fabiobrasileiroo/silakka54-fabio-custom/01-final/previews/preview-carry-67mm.png

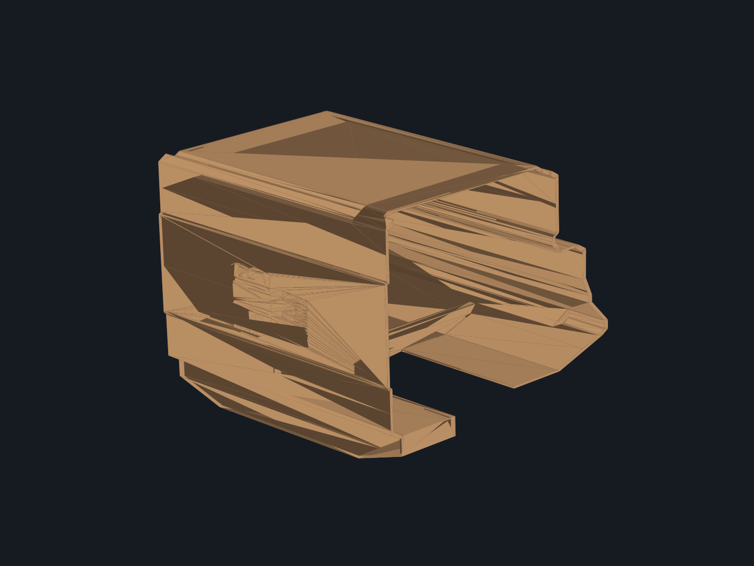
01-final/previews/preview-carry-67mm.png
