fabiobrasileiroo/silakka54-fabio-custom/docs/01-final/previews/preview-base-L.png

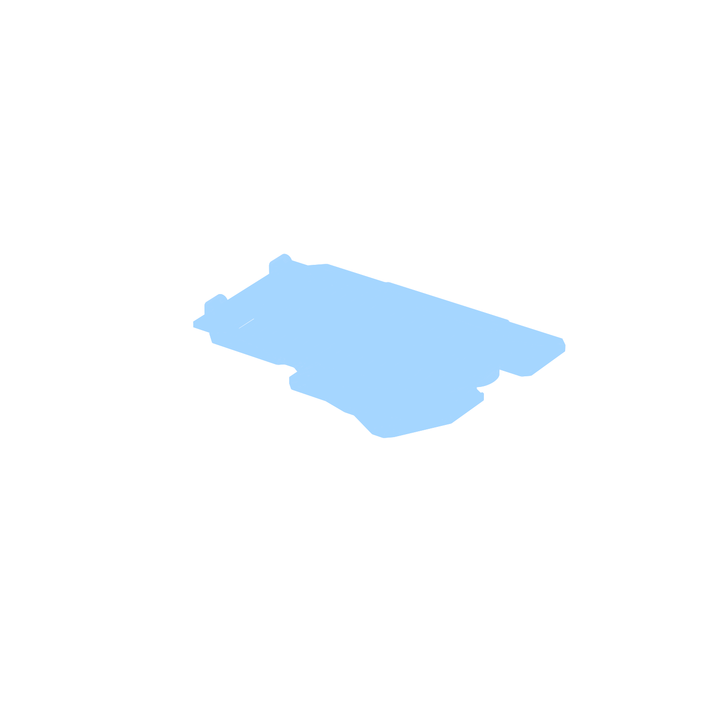
docs/01-final/previews/preview-base-L.png
