fabiobrasileiroo/silakka54-fabio-custom/docs/01-final/previews/preview-carry-case.png

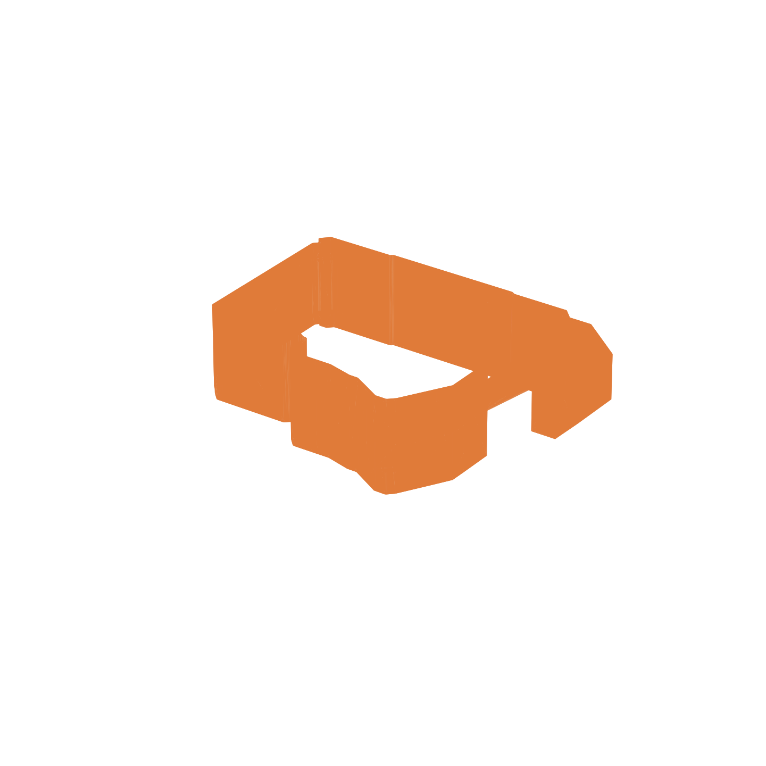
docs/01-final/previews/preview-carry-case.png
