fabiobrasileiroo/silakka54-fabio-custom/docs/01-final/previews/preview-carry-check-engrave.png

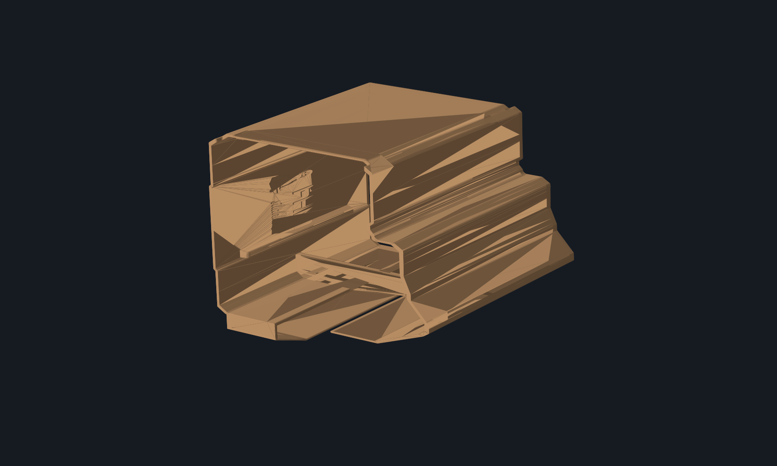
docs/01-final/previews/preview-carry-check-engrave.png
