fabiobrasileiroo/silakka54-fabio-custom/docs/01-final/previews/preview-carry-check-mirror.png

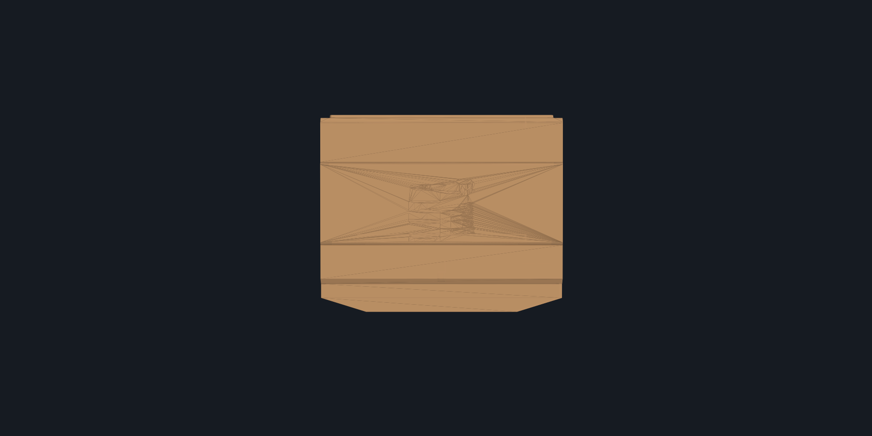
docs/01-final/previews/preview-carry-check-mirror.png
