fabiobrasileiroo/silakka54-fabio-custom/docs/01-final/previews/preview-cover-plaque-RH.png

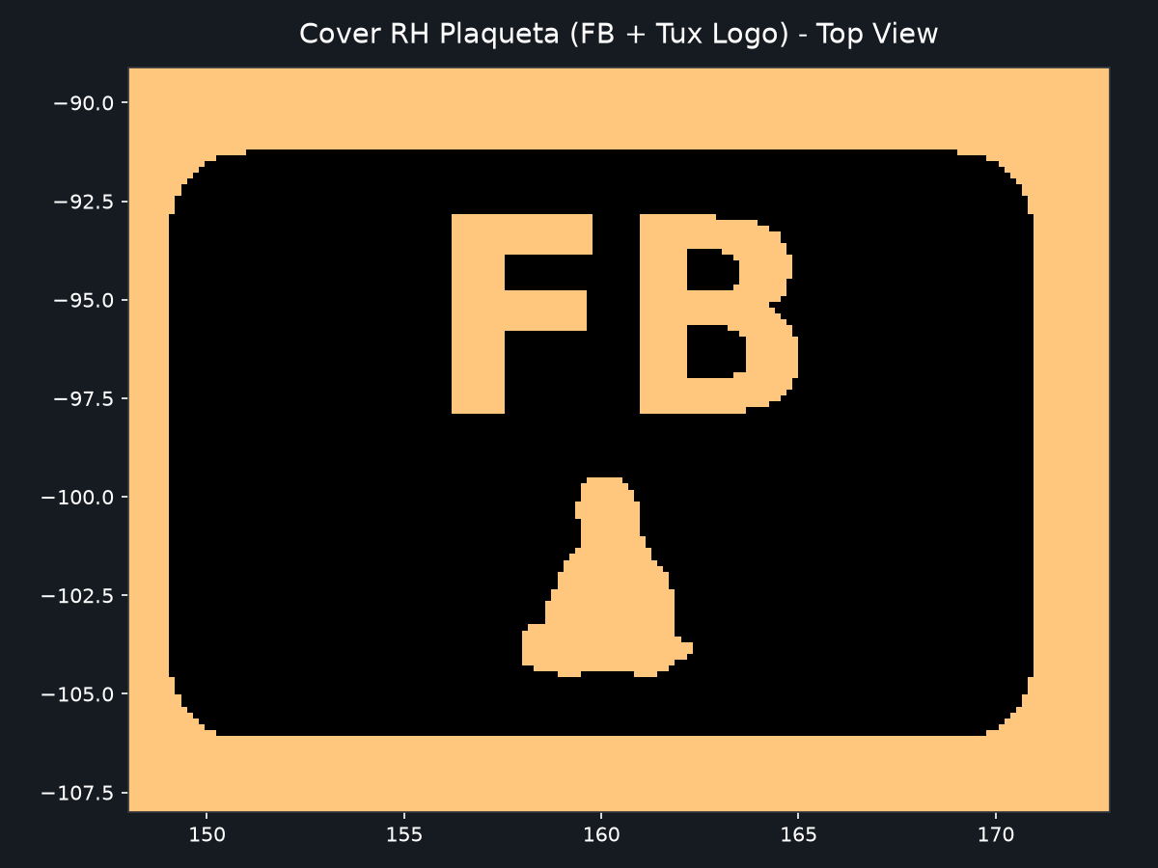
docs/01-final/previews/preview-cover-plaque-RH.png
