fabiobrasileiroo/silakka54-fabio-custom/docs/01-final/previews/preview-FB-Tux-linux-LH.png

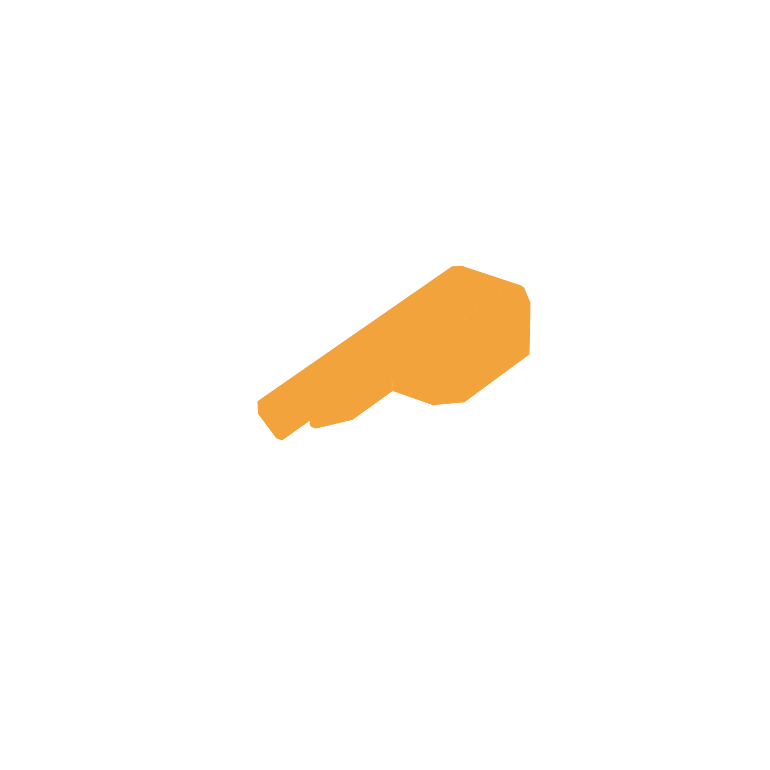
docs/01-final/previews/preview-FB-Tux-linux-LH.png
