fabiobrasileiroo/silakka54-fabio-custom/docs/01-final/previews/preview-FB-Tux-linux-RH.png

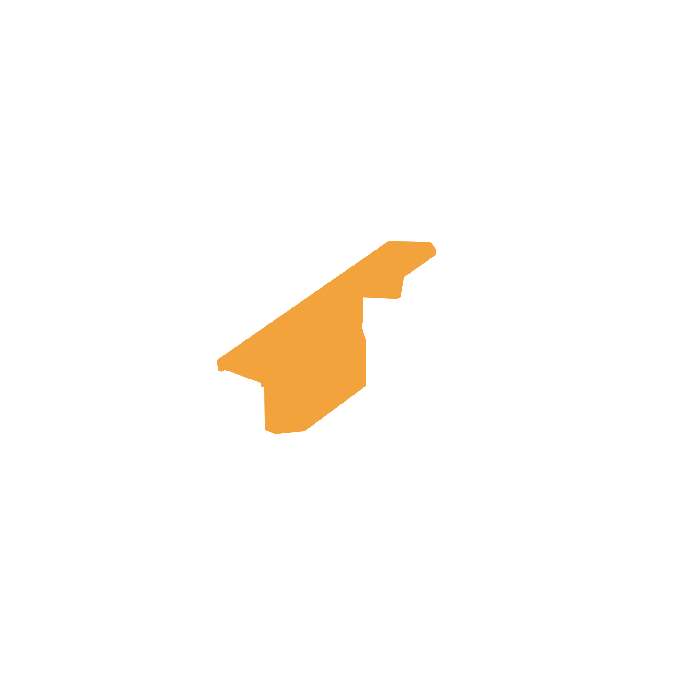
docs/01-final/previews/preview-FB-Tux-linux-RH.png
