fabiobrasileiroo/silakka54-fabio-custom/docs/01-final/previews/preview-inner-frame.png

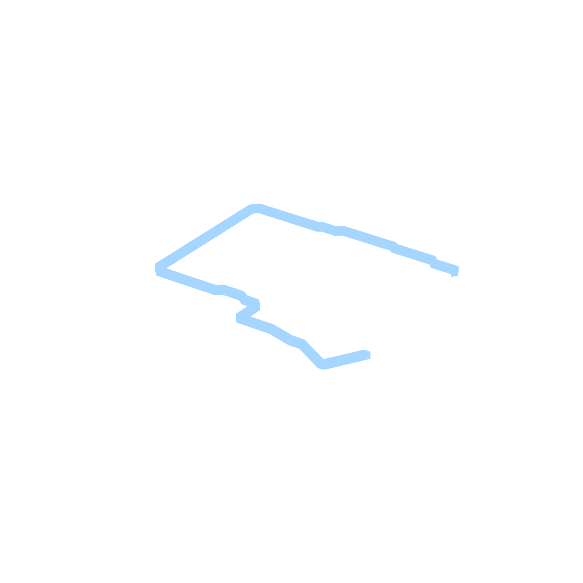
docs/01-final/previews/preview-inner-frame.png
