fabiobrasileiroo/silakka54-fabio-custom/docs/01-final/previews/preview-java-RH.png

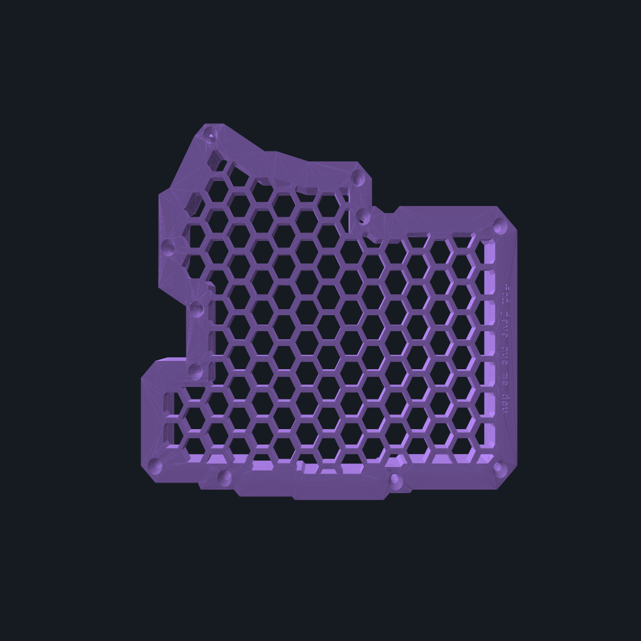
docs/01-final/previews/preview-java-RH.png
