fabiobrasileiroo/silakka54-fabio-custom/docs/01-final/previews/preview-js-LH.png

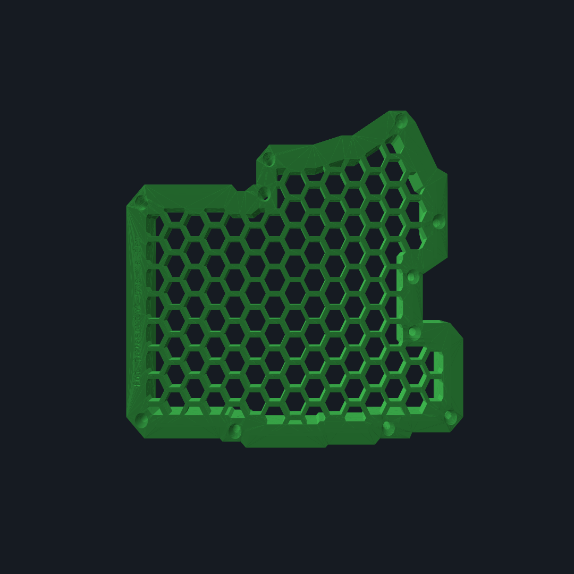
docs/01-final/previews/preview-js-LH.png
