fabiobrasileiroo/silakka54-fabio-custom/docs/01-final/previews/preview-palm-rest-LH.png

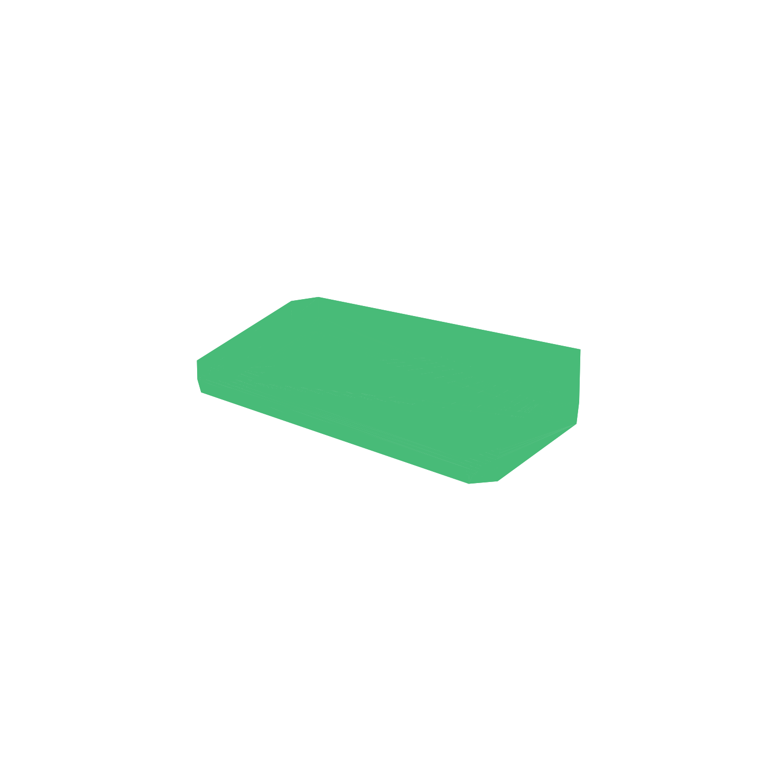
docs/01-final/previews/preview-palm-rest-LH.png
