fabiobrasileiroo/silakka54-fabio-custom/docs/01-final/previews/preview-slim-bottom-LH.png

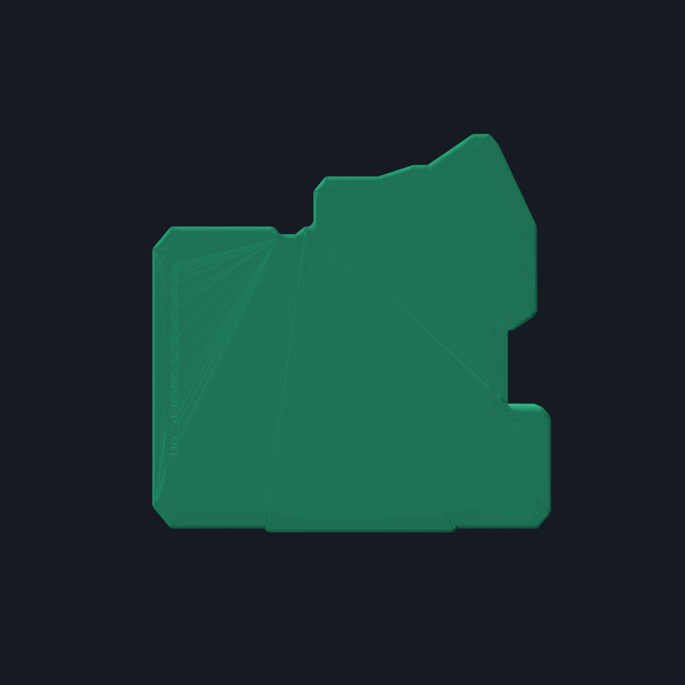
docs/01-final/previews/preview-slim-bottom-LH.png
