fabiobrasileiroo/silakka54-fabio-custom/docs/01-final/previews/preview-slim-bottom-RH.png

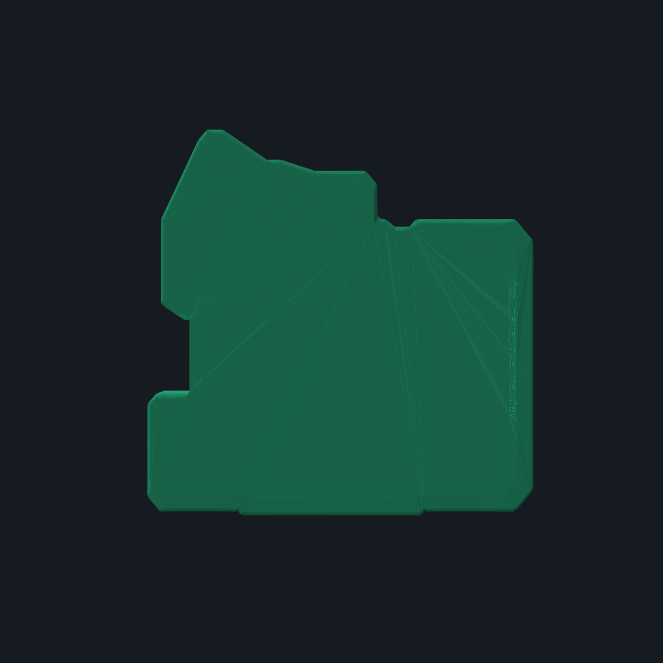
docs/01-final/previews/preview-slim-bottom-RH.png
