fabiobrasileiroo/silakka54-fabio-custom/docs/01-final/previews/preview-slim-check-unmirror.png

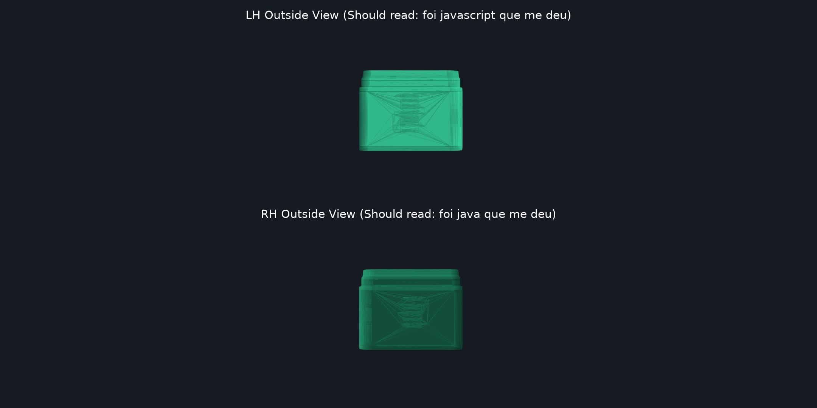
docs/01-final/previews/preview-slim-check-unmirror.png
