fabiobrasileiroo/silakka54-fabio-custom/docs/01-final/previews/preview-slim-cover-bridge.png

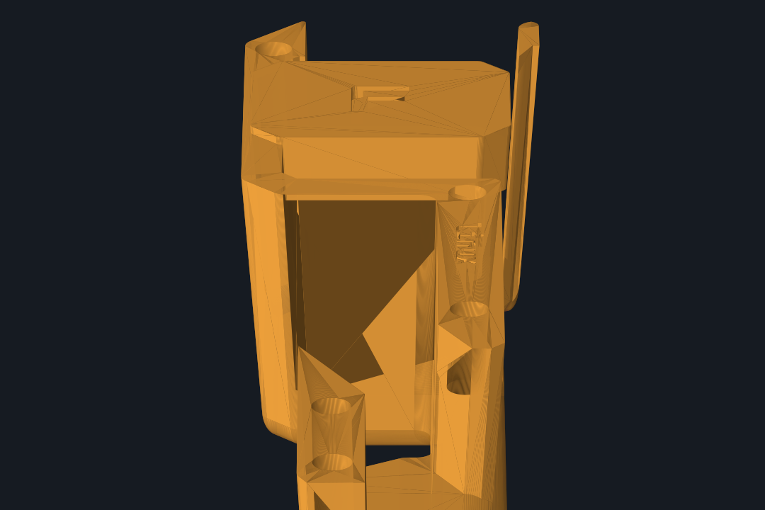
docs/01-final/previews/preview-slim-cover-bridge.png
