fabiobrasileiroo/silakka54-fabio-custom/docs/01-final/previews/preview-slim-plaque-LH.png

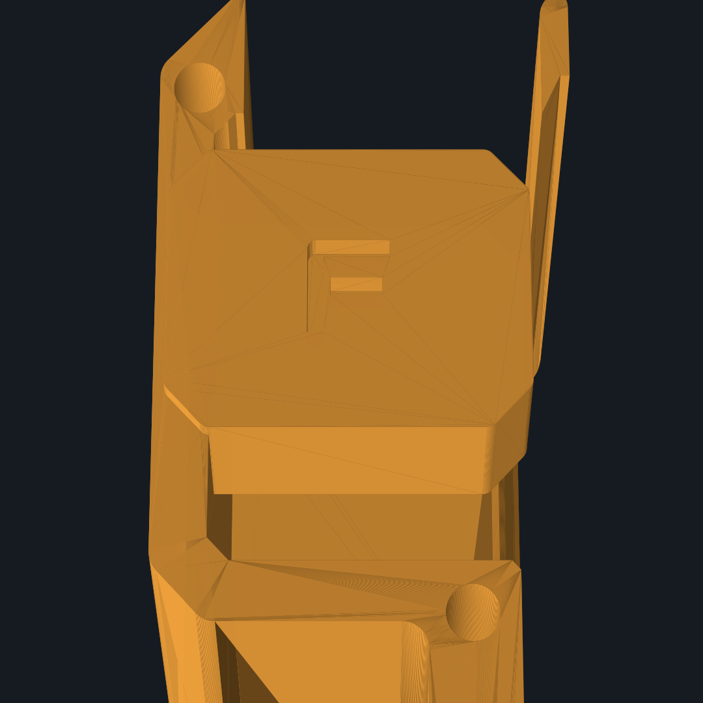
docs/01-final/previews/preview-slim-plaque-LH.png
