fabiobrasileiroo/silakka54-fabio-custom/docs/01-final/previews/preview-slim-plaque-RH.png

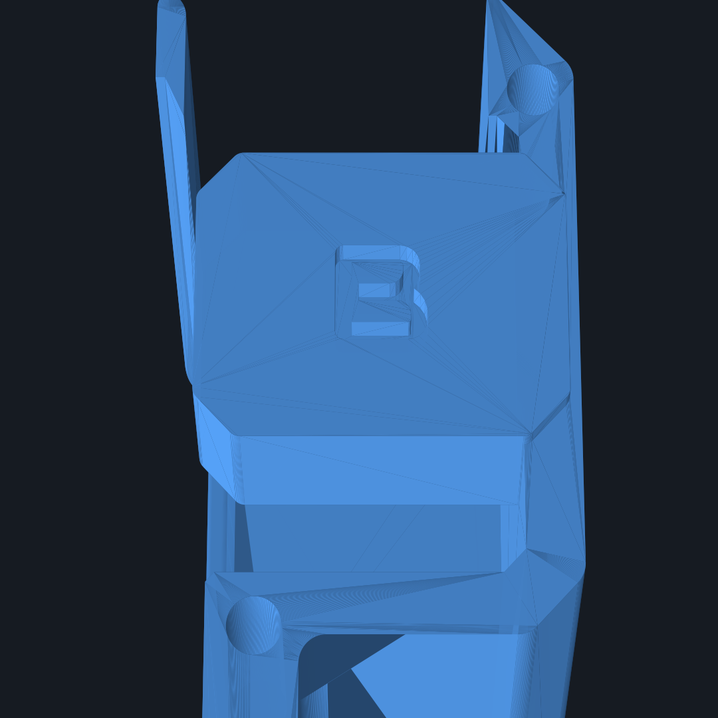
docs/01-final/previews/preview-slim-plaque-RH.png
