fabiobrasileiroo/silakka54-fabio-custom/docs/01-final/previews/preview-wedge.png

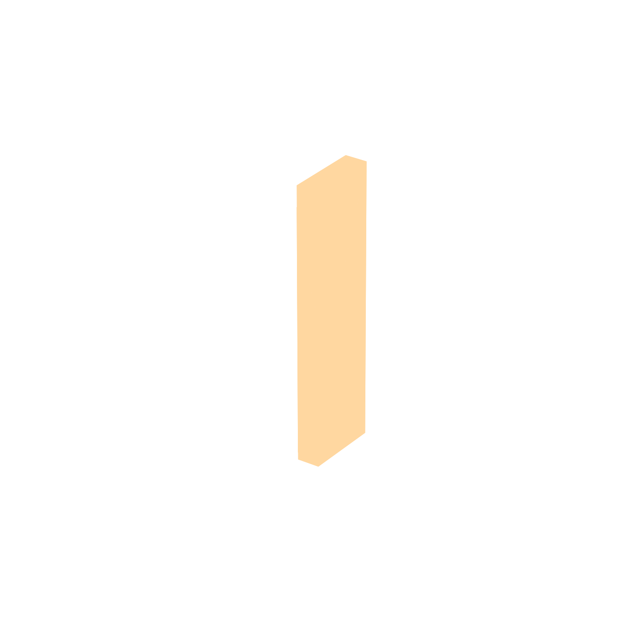
docs/01-final/previews/preview-wedge.png
