fabiobrasileiroo/silakka54-fabio-custom/docs/01-final/previews/tux-classic-feet.png

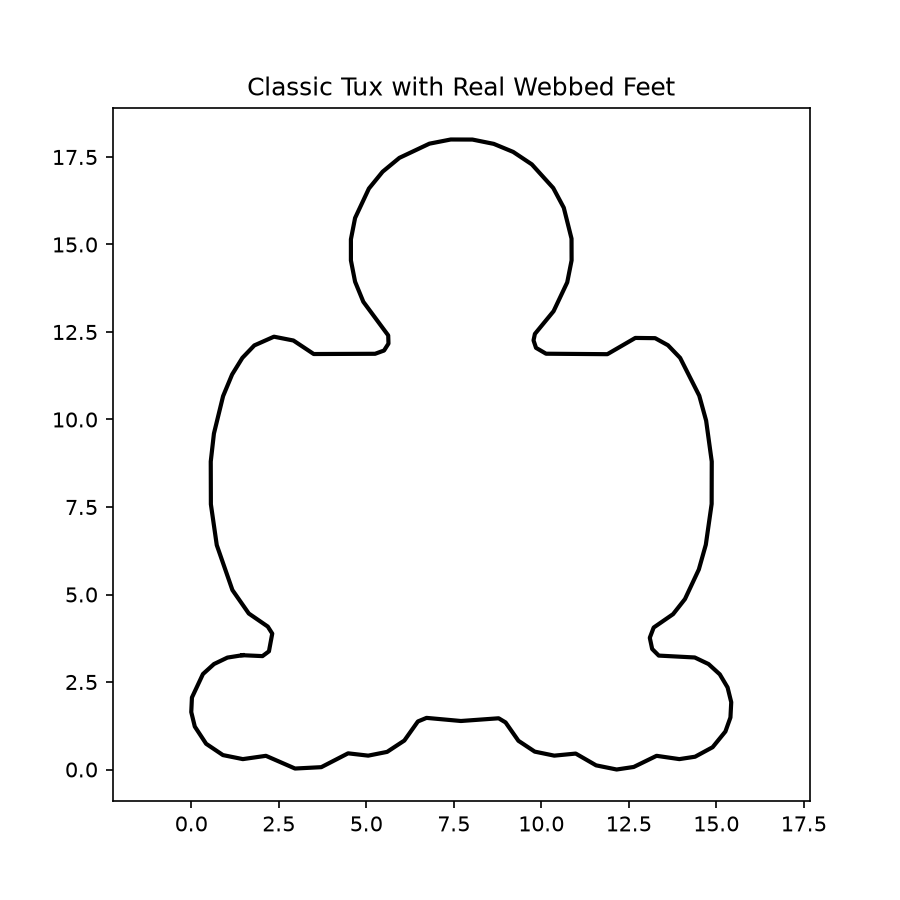
docs/01-final/previews/tux-classic-feet.png
