fabiobrasileiroo/silakka54-fabio-custom/docs/01-final/previews/tux-feet-clean.png

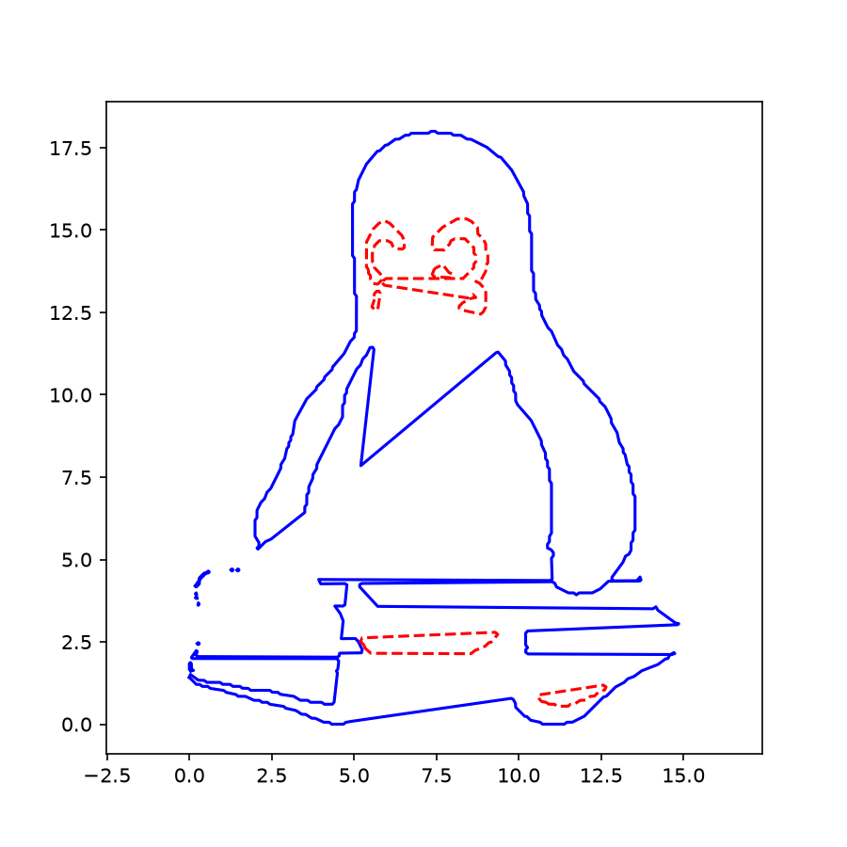
docs/01-final/previews/tux-feet-clean.png
