fabiobrasileiroo/silakka54-fabio-custom/docs/01-final/previews/tux-feet-preview.png

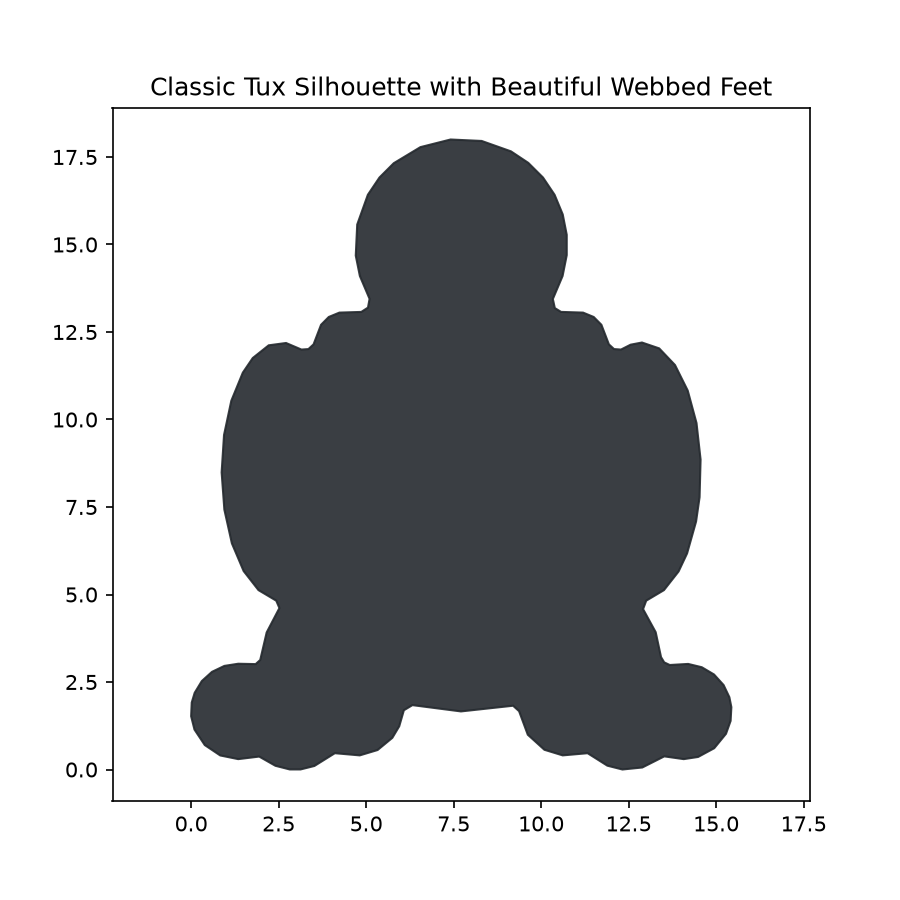
docs/01-final/previews/tux-feet-preview.png
