fabiobrasileiroo/silakka54-fabio-custom/docs/01-final/previews/tux-vector-perfect.png

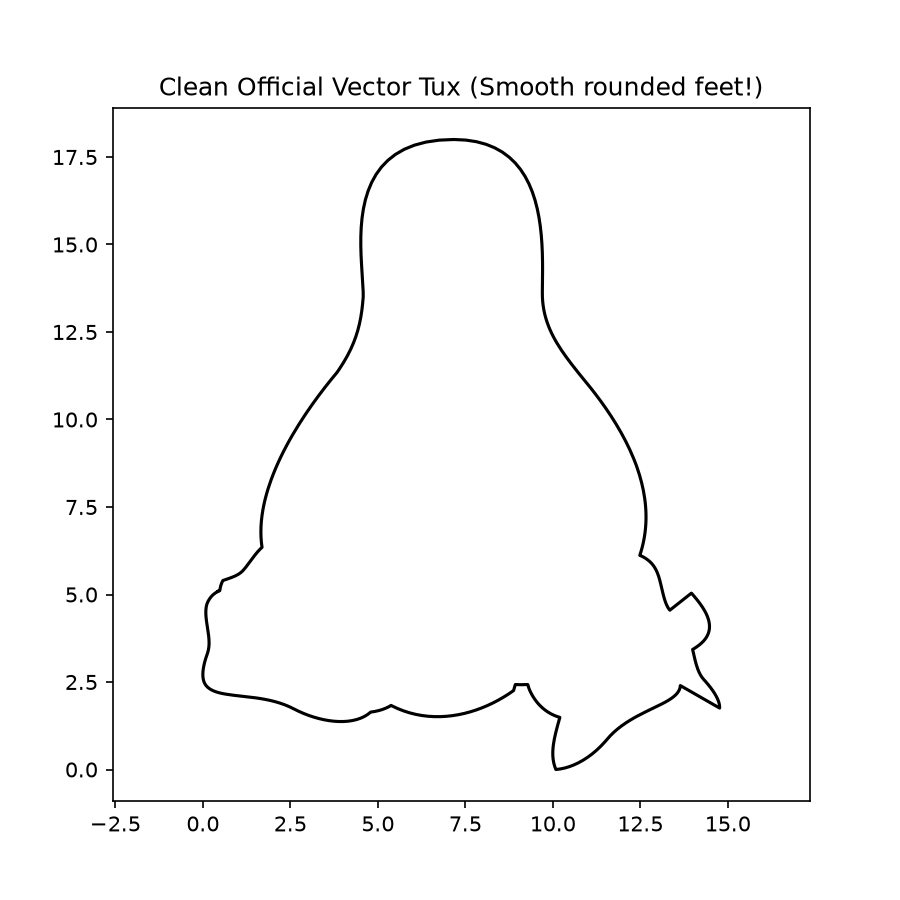
docs/01-final/previews/tux-vector-perfect.png
