fabiobrasileiroo/silakka54-fabio-custom/docs/01-final/carry-tent-2em1/silakka54_right_base_support.stl

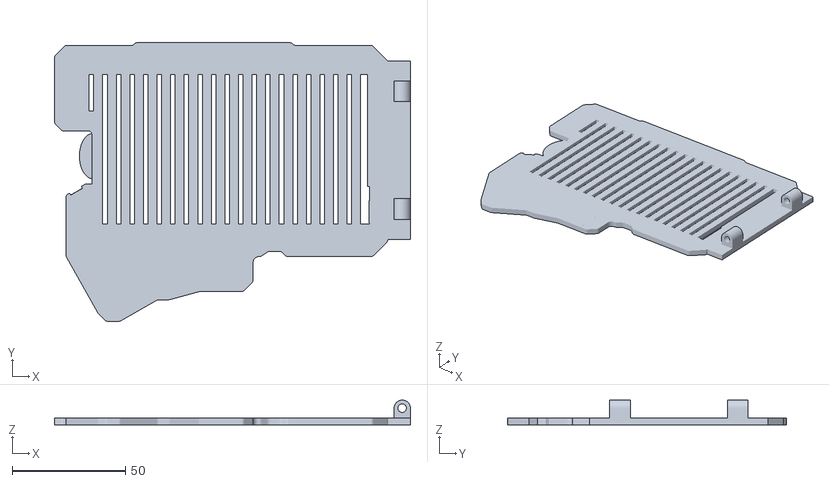
[picture p45: CAD file, 2026-08-10]
docs/01-final/carry-tent-2em1/silakka54_right_base_support.stl
157.3 x 123.1 x 11.0
