fabiobrasileiroo/silakka54-fabio-custom/docs/01-final/carry-tent-2em1/silakka54_left_side_shell.stl

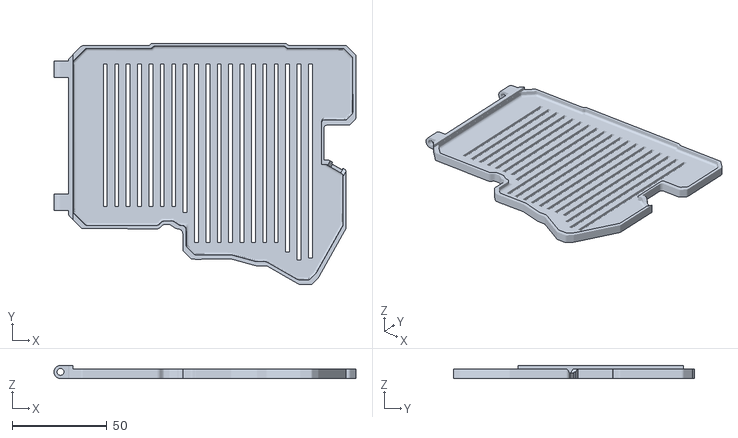
[picture p46: CAD file, 2026-08-10]
docs/01-final/carry-tent-2em1/silakka54_left_side_shell.stl
159.0 x 127.1 x 7.00
