fabiobrasileiroo/silakka54-fabio-custom/docs/01-final/carry-tent-2em1/silakka54_right_side_shell.stl

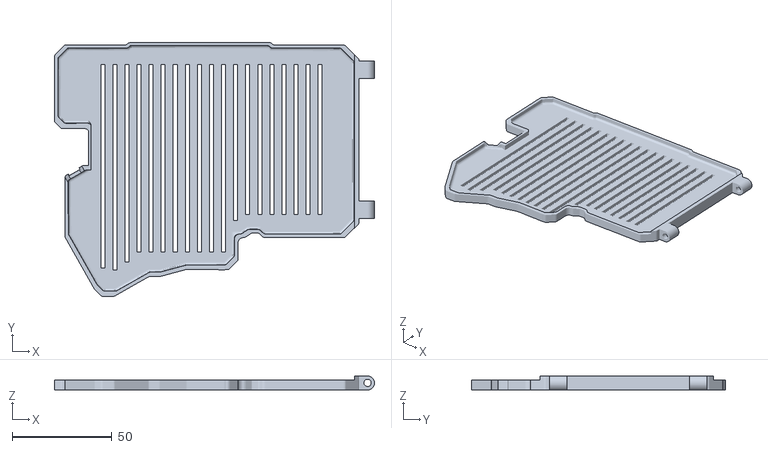
[picture p47: CAD file, 2026-08-10]
docs/01-final/carry-tent-2em1/silakka54_right_side_shell.stl
160.4 x 127.1 x 7.00
