fabiobrasileiroo/silakka54-fabio-custom/docs/01-final/carry-tent-2em1/silakka54-case.stl

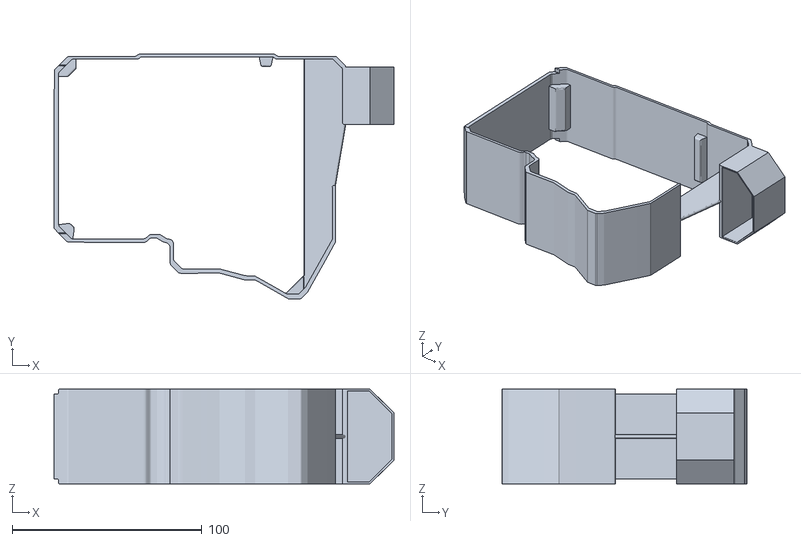
[picture p48: CAD file, 2026-08-10]
docs/01-final/carry-tent-2em1/silakka54-case.stl
179.0 x 128.9 x 50.0
