fabiobrasileiroo/silakka54-fabio-custom/docs/img/silakka54-assembled.jpg

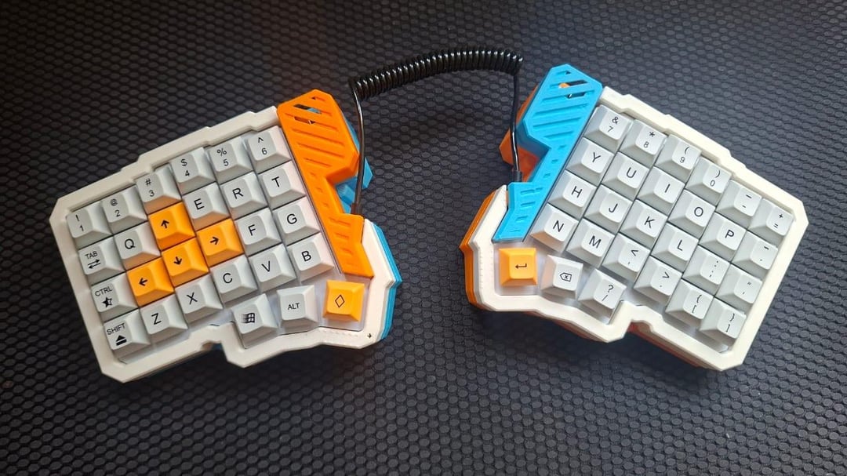
docs/img/silakka54-assembled.jpg
