fabiobrasileiroo/silakka54-fabio-custom/docs/01-final/previews/tux-debug.png

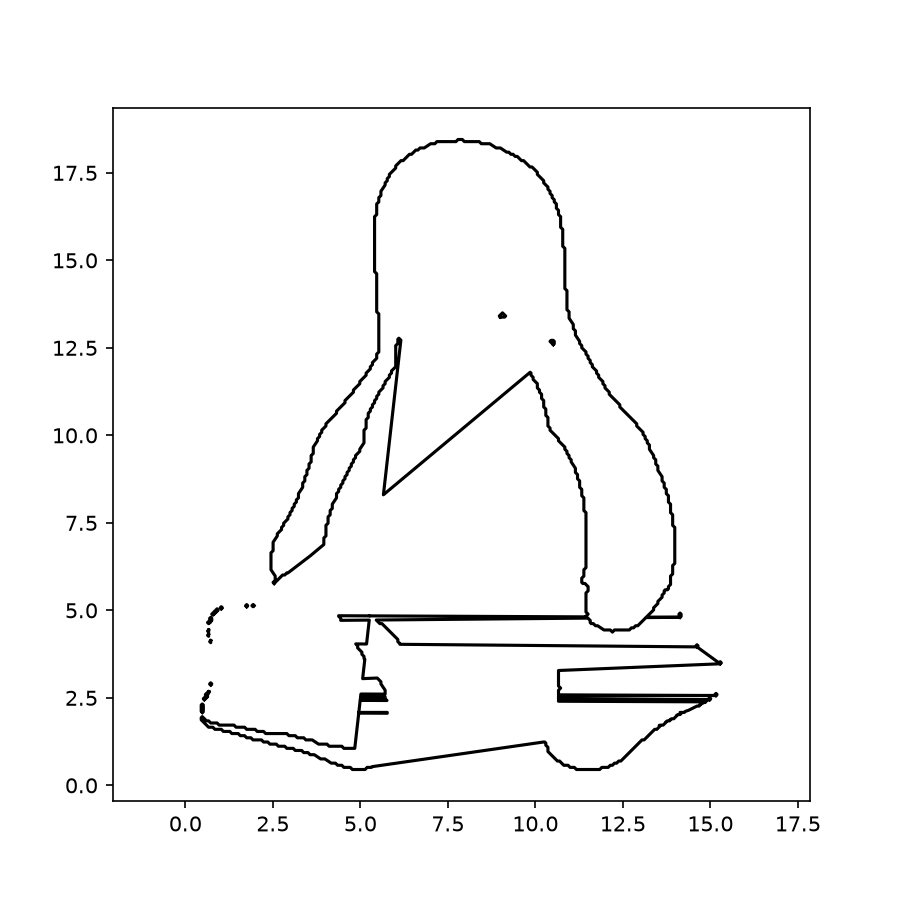
docs/01-final/previews/tux-debug.png
